bt-soft/pico-zero-ili9488-gps-spedometer/Docs/TFT_eSPI/drawing_dc793e47-cfa5-4376-a1f5-dbce3622f55d.webp

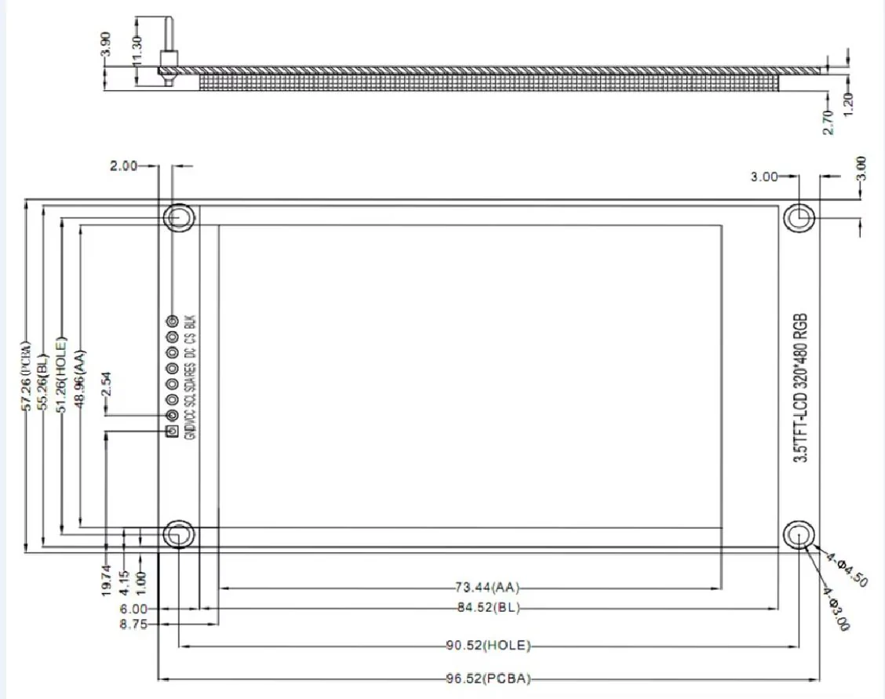
Docs/TFT_eSPI/drawing_dc793e47-cfa5-4376-a1f5-dbce3622f55d.webp
