bt-soft/pico-zero-ili9488-gps-spedometer/src/ScreenDebugSetup.cpp

#include "ScreenDebugSetup.h"
#include "Config.h"
#include "Utils.h"
#include "defines.h"

#include "GpsManager.h"
extern GpsManager *gpsManager;

/**
 * UI komponensek elhelyezése
 */
void ScreenDebugSetup::layoutComponents() {

    // Függőlegesen egymás alá
    int btnW = 180;
    int btnH = 60;
    int btnX = (::SCREEN_W - btnW) / 2;
    int btnY = 60;
    int btnGap = 20;

    // LED gomb
    int row = 0;
    addChild(std::make_shared<UIButton>(                                                                      //
        10,                                                                                                   // id
        Rect(btnX, btnY + row * (btnH + btnGap), btnW, btnH),                                                 // rect
        "Pico-Zero LED",                                                                                      // label
        UIButton::ButtonType::Toggleable,                                                                     // type
        config.data.debugGpsSerialOnInternalFastLed ? UIButton::ButtonState::On : UIButton::ButtonState::Off, // Kezdeti állapot
        [this](const UIButton::ButtonEvent &event) {
            if (event.state == UIButton::EventButtonState::On || event.state == UIButton::EventButtonState::Off) {
                config.data.debugGpsSerialOnInternalFastLed = event.state == UIButton::EventButtonState::On;
                config.checkSave();
            }
        }) //
    );

    // GPS On Serial
    row++;
    addChild(std::make_shared<UIButton>(                      //
        11,                                                   // id
        Rect(btnX, btnY + row * (btnH + btnGap), btnW, btnH), // rect
        "GPS On Serial",                                      // label
        UIButton::ButtonType::Toggleable,                     // type
#ifdef __DEBUG
        config.data.debugGpsSerialData ? UIButton::ButtonState::On : UIButton::ButtonState::Off, // Kezdeti állapot
#else
        UIButton::ButtonState::Disabled, // Ha nincs Serial, akkor nincs értelme
#endif
        [this](const UIButton::ButtonEvent &event) {
            if (event.state == UIButton::EventButtonState::On || event.state == UIButton::EventButtonState::Off) {
                config.data.debugGpsSerialData = event.state == UIButton::EventButtonState::On;
                config.checkSave();
            }
        }) //
    );

    // SatDB on Serial
    row++;
    addChild(std::make_shared<UIButton>(                      //
        12,                                                   // id
        Rect(btnX, btnY + row * (btnH + btnGap), btnW, btnH), // rect
        "SatDB On Serial",                                    // label
        UIButton::ButtonType::Toggleable,                     // type
#ifdef __DEBUG
        config.data.debugGpsSatellitesDatabase ? UIButton::ButtonState::On : UIButton::ButtonState::Off, // Kezdeti állapot
#else
        UIButton::ButtonState::Disabled, // Ha nincs Serial, akkor nincs értelme
#endif
        [this](const UIButton::ButtonEvent &event) {
            if (event.state == UIButton::EventButtonState::On || event.state == UIButton::EventButtonState::Off) {
                config.data.debugGpsSatellitesDatabase = event.state == UIButton::EventButtonState::On;
                config.checkSave();
            }
        }) //
    );

    // Back gomb jobb alsó sarokban
    addChild(std::make_shared<UIButton>(                                                                                                                                  //
        1,                                                                                                                                                                //
        Rect(::SCREEN_W - UIButton::DEFAULT_BUTTON_WIDTH, ::SCREEN_H - UIButton::DEFAULT_BUTTON_HEIGHT, UIButton::DEFAULT_BUTTON_WIDTH, UIButton::DEFAULT_BUTTON_HEIGHT), //
        "Back",                                                                                                                                                           //
        UIButton::ButtonType::Pushable,                                                                                                                                   //
        [this](const UIButton::ButtonEvent &event) {
            if (event.state == UIButton::EventButtonState::Clicked) {
                getScreenManager()->goBack();
            }
        }) //
    );
}

/**
 *
 */
void ScreenDebugSetup::drawContent() {
    tft.fillScreen(TFT_BLACK);
    tft.setTextDatum(MC_DATUM);
    tft.setTextSize(1);
    tft.setFreeFont(&FreeSansBold18pt7b);
    tft.setTextColor(TFT_CYAN, TFT_BLACK);
    tft.drawString("Debug Settings", ::SCREEN_W / 2, 20);
    tft.setFreeFont();
    // ...ide jönnek majd a beállítási gombok/ValueChangeDialog...
}
