bt-soft/pico-zero-ili9488-gps-spedometer/include/UIDialogBase.h

#pragma once

#include <functional>

#include "UIButton.h"
#include "UIContainerComponent.h"

// Előre deklarációk
class UIScreen;

class UIDialogBase : public UIContainerComponent {
  public:
    static constexpr const uint8_t DIALOG_DEFAULT_CLOSE_BUTTON_ID = 254; // Alapértelmezett bezáró gomb ID

    enum class DialogResult {
        None,
        Accepted, // OK, Yes, stb.
        Rejected, // Cancel, No, stb.
        Dismissed // 'X' gombbal vagy programatikusan bezárva
    };

    using DialogCallback = std::function<void(UIDialogBase *, DialogResult)>;

  protected:
    UIScreen *parentScreen;                          // A képernyő, amely megjelenítette ezt a dialógust
    const char *title;                               // Dialógus címe
    DialogCallback callback = nullptr;               // Callback, amelyet a dialógus eseményeihez használunk, DialogResult-ot ad vissza
    bool veilDrawn = false;                          // Fátyol rajzolásának állapota
    bool autoClose = true;                           // Automatikus bezárás a gombok megnyomásakor
    std::shared_ptr<UIButton> closeButton = nullptr; // Bezáró gomb    // Deferred close mechanism to prevent nested callback chains

    struct DeferredClose {
        bool pending = false;
        DialogResult result = DialogResult::Dismissed;
        std::shared_ptr<UIDialogBase> chainCloseDialog = nullptr; // Additional dialog to close in chain
    };
    DeferredClose deferredClose;

    // Dialógus elrendezési konstansok
    static constexpr uint16_t HEADER_HEIGHT = 28;                                  // Fejléc magassága
    static constexpr uint16_t PADDING = 5;                                         // Belső margó
    static constexpr uint16_t BUTTONS_GAP = 30;                                    // Bombok közötti rés
    static constexpr uint16_t BORDER_RADIUS = 8;                                   // Saroklekerekítés
    static constexpr uint16_t CLOSE_BUTTON_SIZE = HEADER_HEIGHT - 2 * PADDING - 2; // Bezáró gomb mérete
    static constexpr uint16_t VEIL_COLOR = TFT_DARKGREY;                           // Fátyol színe (lehetne tft.color565(30,30,30) egy sötétebbért)

    static constexpr uint16_t DEFAULT_HEADER_HEIGHT = HEADER_HEIGHT;
    static constexpr uint16_t DEFAULT_HEADER_HEIGHT_WITH_TITLE = HEADER_HEIGHT;
    static constexpr uint16_t DEFAULT_HEADER_HEIGHT_NO_TITLE = HEADER_HEIGHT; // Leszármazottaknak felüldefiniálható metódusok a tartalom és lábléc létrehozásához
    virtual void createDialogContent() {}
    virtual void layoutDialogContent() {} // Elrendezéshez, ha szükséges

    // Belső segéd metódusok
    void createCloseButton();
    void drawVeil();

    bool topDialog = false; // Jelzi, hogy ez a dialógus a legfelső (legutolsó) a stackben

  public:
    UIDialogBase(UIScreen *parentScreen, const char *title, const Rect &bounds, const ColorScheme &cs = ColorScheme::defaultScheme());
    virtual ~UIDialogBase() override = default;
    virtual void show();
    virtual void close(DialogResult result = DialogResult::Dismissed); // Deferred close mechanism
    void deferClose(DialogResult result = DialogResult::Dismissed);
    void deferChainClose(DialogResult result, std::shared_ptr<UIDialogBase> chainDialog);
    void processDeferredClose();

    // Header magasság lekérése (tartalom pozicionálásához)
    uint16_t getHeaderHeight() const { return HEADER_HEIGHT; }

    void setDialogCallback(DialogCallback cb) { callback = cb; }

    void setAutoClose(bool autoClose) { autoClose = autoClose; }
    bool getAutoClose() const { return autoClose; }

    // UIContainerComponent metódusok felülírása
    virtual void draw() override; // Virtual, hogy a leszármazottak is felülírhassák helyesen
    virtual void markForRedraw(bool markChildren = false) override;

    // A veilDrawn flag resetelése
    void resetVeilDrawnFlag() { veilDrawn = false; }

    /**
     * @brief Touch esemény kezelése, amely először a gyerek komponenseken próbálkozik,
     * majd ha egyik sem, akkor maga a UIDialogBase kezeli.
     * @param event A touch esemény, amely tartalmazza a koordinátákat és a lenyomás állapotát
     */
    virtual bool handleTouch(const TouchEvent &event) override;

    /**
     * @brief Rajzolja a dialógus hátterét és fejlécét.
     */
    virtual void drawSelf() override;

    /**
     * @brief Ellenőrzi, hogy ez a dialógus a legfelső (legutolsó) a stackben.
     * @return true, ha ez a dialógus a legfelső, false ha nem
     */
    inline bool isTopDialog() const { return topDialog; }

    /**
     * @brief Beállítja, hogy ez a dialógus a legfelső legyen a stackben.
     * @param isTop true, ha ez a dialógus a legfelső, false ha nem
     */
    inline void setTopDialog(bool isTop) { topDialog = isTop; }

    /**
     * @brief Visszaadja az összes dialógus gombot (kivéve a bezáró X gombot).
     * @return A gombok listája shared_ptr-ekben. Alapértelmezetten üres lista.
     * @details Ez a virtuális metódus lehetővé teszi, hogy a leszármazott osztályok
     * egységesen visszaadhassák az összes gombj aikat egy listában.
     * A closeButton (X gomb) automatikusan ki van zárva.
     */
    virtual std::vector<std::shared_ptr<UIButton>> getButtonsList() const { return {}; }
};
