bt-soft/pico-zero-ili9488-gps-spedometer/include/SatelliteDb.h

#pragma once

#include <TinyGPS++.h>
#include <algorithm>
#include <list>
#include <vector>

class SatelliteDb {
  public:
    struct SatelliteData {
        uint8_t prn;
        int16_t elevation;
        int16_t azimuth;
        int16_t snr;
        unsigned long timeStamp;

        // Konstruktor
        SatelliteData(uint8_t p, int16_t e, int16_t a, int16_t s, unsigned long t = 0) : prn(p), elevation(e), azimuth(a), snr(s), timeStamp(t) {}
    };

    typedef enum { NONE, BY_PRN, BY_SNR } SortType_t;

    SatelliteDb();
    ~SatelliteDb() = default; // std::list automatikusan felszabadítja a memóriát

    uint8_t countSats() const;
    SatelliteData *searchSat(uint8_t prnNo);
    void deleteSat(uint8_t prn);
    void deleteUntrackedSatellites();
    void insertSatellite(uint8_t prn, int16_t elevation, int16_t azimuth, int16_t snr);
    void sortSatellites();
    void clear();

    // Thread-safe read-only access for UI (Core0)
    std::vector<SatelliteData> getSnapshotForUI(SortType_t sortType = NONE) const;
    uint8_t countSatsForUI() const;

    // Iterator támogatás a külső kód számára
    auto begin() { return satellites.begin(); }
    auto end() { return satellites.end(); }
    auto begin() const { return satellites.begin(); }
    auto end() const { return satellites.end(); }

    void debugSatDb(uint8_t num_sats_in_view);

  private:
    std::list<SatelliteData> satellites;

    // Segédfüggvény a kereséshez
    auto findSatellite(uint8_t prn) {
        return std::find_if(satellites.begin(), satellites.end(), [prn](const SatelliteData &sat) { return sat.prn == prn; });
    }
};
