bt-soft/pico-zero-ili9488-gps-spedometer/include/ScreenInfo.h

#pragma once

#include "UIButton.h"
#include "UIScreen.h"

/**
 * @brief Info képernyő osztály
 */
class ScreenInfo : public UIScreen {

  public:
    /**
     * @brief ScreenInfo konstruktor
     */
    ScreenInfo();

    virtual ~ScreenInfo() = default;

    /**
     * @brief Kirajzolja a képernyő saját tartalmát
     */
    virtual void drawContent() override;

    /**
     * @brief Loop hívás felülírása
     * animációs vagy egyéb saját logika végrehajtására
     * @note Ez a metódus nem hívja meg a gyerek komponensek loop-ját, csak saját logikát tartalmaz.
     */
    virtual void handleOwnLoop() override;

  private:
    uint16_t textPadding;
    uint16_t bootTextPadding;
    unsigned long lastUpdated;

    // String optimalizálás: egyetlen buffer az értékek formázásához
    char valueBuffer[64];

    /**
     * @brief UI komponensek létrehozása és elhelyezése
     */
    void layoutComponents();
};
