bt-soft/pico-zero-ili9488-gps-spedometer/include/ScreenSats.h

#pragma once

#include <TFT_eSPI.h>

#include "SatelliteDb.h"
#include "UIButton.h"
#include "UIScreen.h"
#include "defines.h"

/**
 * @brief Műholdak képernyő
 *
 * Megjeleníti a GPS műholdak részletes információit táblázatosan és vizuálisan.
 */
class ScreenSats : public UIScreen {
  public:
    /**
     * @brief Konstruktor
     */
    ScreenSats();

    /**
     * @brief Destruktor
     */
    ~ScreenSats();

  protected:
    /**
     * @brief Kirajzolja a képernyő saját tartalmát
     */
    void drawContent() override;

    /**
     * @brief Kezeli a képernyő saját ciklusát
     */
    void handleOwnLoop() override;

  private:
    // Korábbi adatok tárolása a változások detektálásához
    std::vector<SatelliteDb::SatelliteData> lastSatellites;
    uint8_t lastSatCount;
    bool firstDraw;

    // Rendezési beállítások
    SatelliteDb::SortType_t currentSortType;
    bool sortOrderChanged;

    // String optimalizálás: buffer az értékek megjelenítéséhez
    char valueBuffer[32];

    /**
     * @brief UI komponensek elhelyezése
     */
    void layoutComponents();

    /**
     * @brief Címsor rajzolása
     */
    void drawTitle();

    /**
     * @brief Műholdak táblázatának rajzolása a bal oldalon
     */
    void drawSatelliteTable();

    /**
     * @brief Műholdak vizuális megjelenítése koncentrikus körben
     */
    void drawSatelliteCircle();

    /**
     * @brief Egy műhold rajzolása a körön
     */
    void drawSatelliteOnCircle(int16_t centerX, int16_t centerY, int16_t maxRadius, const SatelliteDb::SatelliteData &sat);

    /**
     * @brief Ellenőrzi, hogy változtak-e a műhold adatok
     */
    bool satelliteDataChanged(const std::vector<SatelliteDb::SatelliteData> &currentSats, uint8_t currentSatCount);

    /**
     * @brief Visszaadja a SNR értékhez tartozó színt
     */
    uint32_t getColorBySnr(uint8_t snr);

    /**
     * @brief Érintés kezelése
     */
    bool handleTouch(const TouchEvent &event) override;

    /**
     * @brief PRN oszlop fejléc kattintásának kezelése
     */
    void handlePrnHeaderClick();

    /**
     * @brief SNR oszlop fejléc kattintásának kezelése
     */
    void handleSnrHeaderClick();
};
