bt-soft/pico-zero-ili9488-gps-spedometer/include/TraffipaxManager.h

#pragma once

#include <Arduino.h>

#include "defines.h"

#define MAX_TRAFIPAX_COUNT 400
#define MAX_CITY_LEN 25
#define MAX_STREET_LEN 30

class TraffipaxManager {
  public:
    struct TraffipaxRecord {
        char city[MAX_CITY_LEN];
        char street_or_km[MAX_STREET_LEN];
        double lat;
        double lon;
    };

    constexpr static const char *CSV_FILE_NAME = "/trafipaxes.csv";

    TraffipaxManager();

    // Fájl kezelés/betöltés
    boolean checkFile(const char *filename);
    void loadFromCSV(const char *filename);
    int count() const;

    // Trafipax riasztás - csak közeledés esetén riaszt
    const TraffipaxRecord *checkTraffipaxApproach(double currentLat, double currentLon, double alertDistanceMeters);

    // Legközelebbi trafipax keresése távolsággal együtt
    const TraffipaxRecord *getClosestTraffipax(double currentLat, double currentLon, double &outDistance) const;

    // Demo funkciók
    void startDemo();
    void processDemo();
    bool isDemoActive() const;
    bool getDemoCoords(double &lat, double &lon) const;

  private:
    TraffipaxRecord traffipaxList[MAX_TRAFIPAX_COUNT];
    int traffipaxCount = 0;

    // Távolság követés közeledés detektáláshoz
    double lastLat = 0.0;
    double lastLon = 0.0;
    int lastClosestTraffipaxIdx = -1;
    double lastDistance = 999999.0;

    // String optimalizálás: buffer a koordináták formázásához
    char coordBuffer[32];

    // Demo traffipax közeledés/távolodás szimulálása működés közben
    struct TraffipaxDemo {
        bool isActive = false;
        unsigned long startTime = 0;
        unsigned long currentPhase = 0;

        // Demo koordináták
        double currentLat = 0.0;
        double currentLon = 0.0;
        bool hasValidCoords = false;

        // Demo fázisok (másodpercben)
        static constexpr unsigned long PHASE_WAIT = 5;      // 5mp várakozás
        static constexpr unsigned long PHASE_APPROACH = 20; // 15mp közeledés (5-20mp)
        static constexpr unsigned long PHASE_DEPART = 40;   // 20mp távolodás (20-40mp) - lassítva
        static constexpr unsigned long PHASE_END = 45;      // 5mp befejezés (40-45mp)

        // Demo Trafipax koordináták

        // Litér
        // static constexpr double DEMO_TRAFFIPAX_LAT = 47.100934;
        // static constexpr double DEMO_TRAFFIPAX_LON = 18.011792;

        // Hódmezővásárhely
        static double demoTraffipaxLat;
        static double demoTraffipaxLon;
    };

    // Demo objektum
    TraffipaxDemo demo;
};
