bt-soft/pico-zero-ili9488-gps-spedometer/include/ScreenGPSSetup.h

#pragma once

#include "UIScreen.h"

class ScreenGPSSetup : public UIScreen {
  public:
    ScreenGPSSetup() : UIScreen(SCREEN_NAME_GPS_SETUP) { layoutComponents(); }
    void layoutComponents() override;
    void drawContent() override;

  private:
    std::shared_ptr<UIButton> gpsTraffiAlarmDistanceBtn;
};
