bt-soft/pico-zero-ili9488-gps-spedometer/include/IScreenManager.h

#pragma once

class IScreenManager {

  public:
    virtual bool switchToScreen(const char *screenName, void *params = nullptr) = 0;
    virtual bool goBack() = 0;
    virtual bool isCurrentScreenDialogActive() = 0;
};
