bt-soft/pico-zero-ili9488-gps-spedometer/include/ScreenTFTSetup.h

#pragma once

#include "UIScreen.h"
class ScreenTFTSetup : public UIScreen {
  public:
    ScreenTFTSetup() : UIScreen(SCREEN_NAME_TFT_SETUP) { layoutComponents(); }
    void layoutComponents() override;
    void drawContent() override;

  private:
    std::shared_ptr<UIButton> manualBrightnessBtn;
};
