bt-soft/pico-zero-ili9488-gps-spedometer/include/SensorUtils.h

#pragma once

#include <Arduino.h>
#include <DallasTemperature.h>
#include <NonBlockingDallas.h>
#include <OneWire.h>

#include "defines.h"
#include "pins.h"

// Cache konstans
#define SENSORS_CACHE_TIMEOUT_MS (5 * 1000) // 5 másodperc a cache idő

// Cache struktúra
class SensorUtils {
  private:
    float vBusExtValue;            // VBUS KÜLSŐ feszültség utolsó mért értéke (Volt)
    unsigned long vBusExtLastRead; // VBUS utolsó mérésének időpontja (ms)
    bool vBusExtValid;             // VBUS cache érvényessége

    float vSysExtValue;            // VSYS KÜLSŐ feszültség utolsó mért értéke (Volt)
    unsigned long vSysExtLastRead; // VSYS utolsó mérésének időpontja (ms)
    bool vSysExtValid;             // VSYS cache érvényessége

    float coreTemperatureValue;            // Hőmérséklet utolsó mért értéke (Celsius)
    unsigned long coreTemperatureLastRead; // Hőmérséklet utolsó mérésének időpontja (ms)
    bool coreTemperatureValid;             // Hőmérséklet cache érvényessége

    // DS18B20
    static volatile float externalTemperatureValue; // Külső hőmérséklet utolsó mért értéke (Celsius)
    static void handleTemperatureChange(int deviceIndex, int32_t temperatureRAW);

  public:
    SensorUtils();

    /**
     * Inicializálja az osztályt
     */
    void init();

    /**
     * ADC olvasás és VBUS feszültség kiszámítása KÜLSŐ osztóval
     * @return A VBUS mért feszültsége Voltban.
     */
    float readVBusExternal();

    /**
     * ADC olvasás és VSYS feszültség kiszámítása KÜLSŐ osztóval
     * @return A VSYS mért feszültsége Voltban.
     */
    float readVSysExternal();

    /**
     * Kiolvassa a processzor hőmérsékletét
     * @return processzor hőmérséklete Celsius fokban
     */
    float readCoreTemperature();

    /**
     * Kiolvassa a külső hőmérsékletét
     * @return külső hőmérséklete Celsius fokban
     */
    float readExternalTemperature();

    /**
     * Loop
     */
    void loop();
};

// Globális cache példány
extern SensorUtils sensorUtils;
